MattStarfield/HumidiFire/img/hw01.jpg

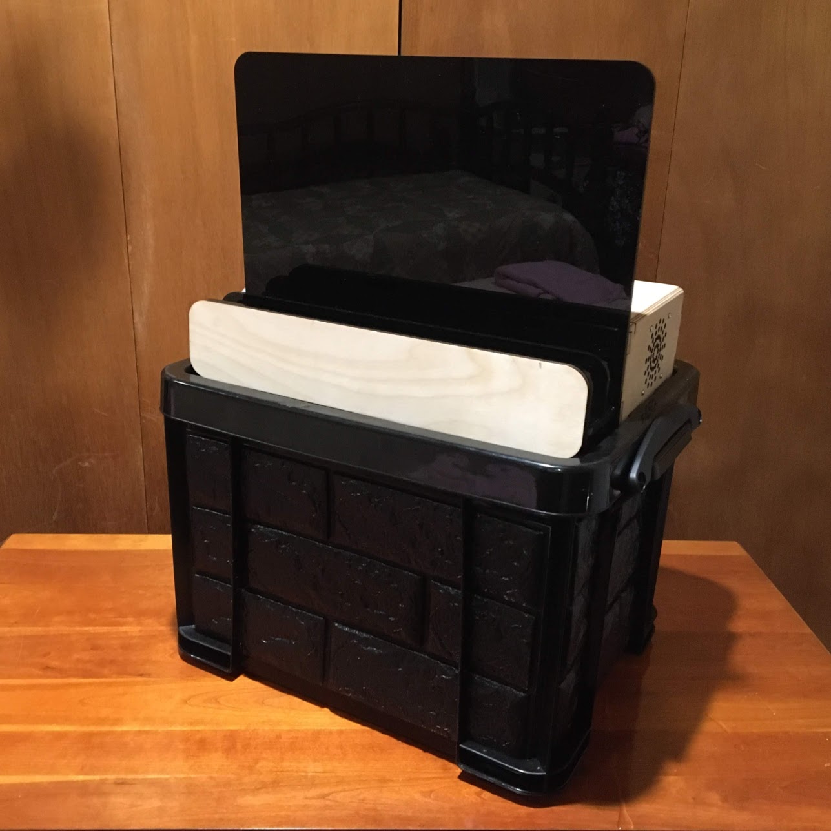
img/hw01.jpg
