MattStarfield/HumidiFire/img/hw02.jpg

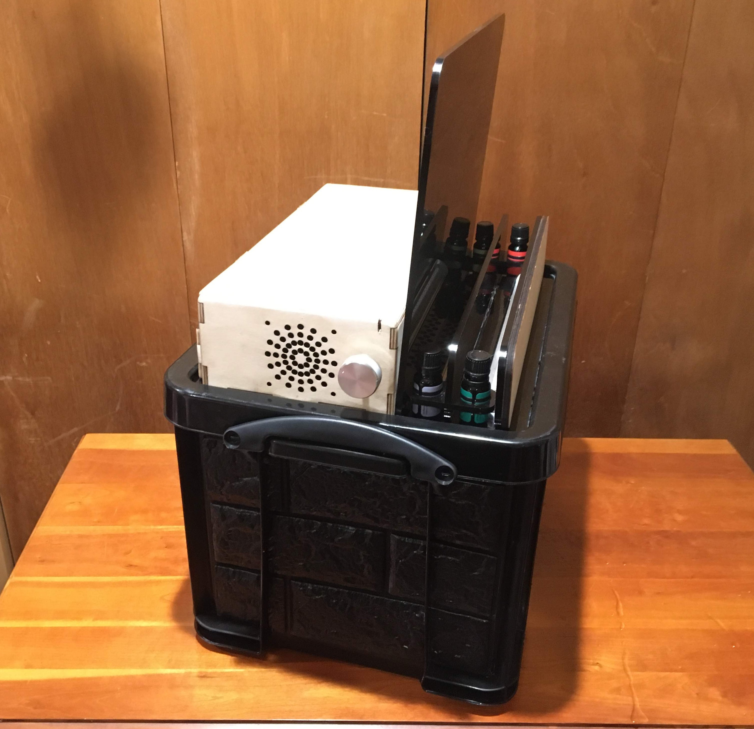
img/hw02.jpg
