MattStarfield/HumidiFire/img/hw03.jpg

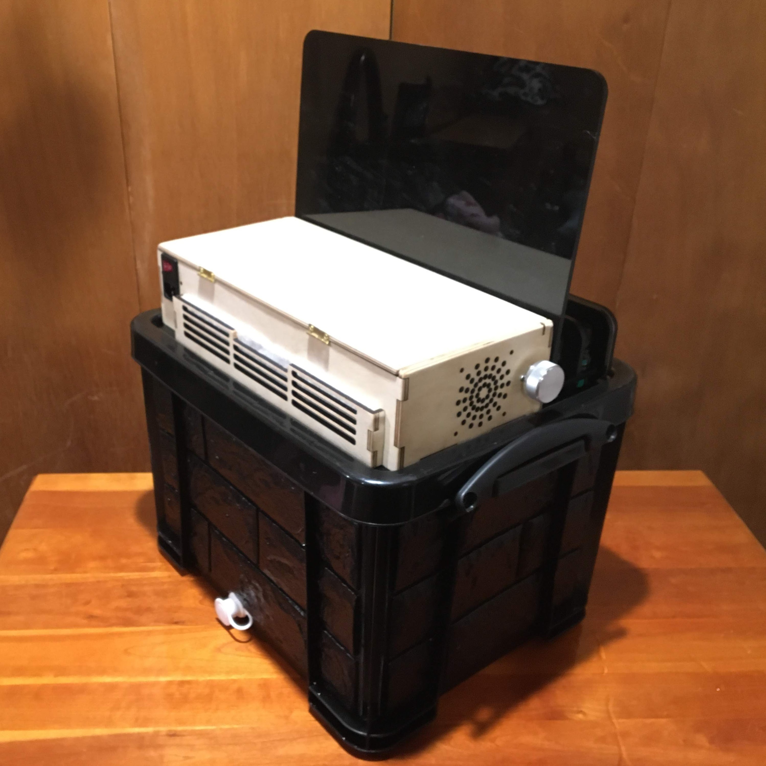
img/hw03.jpg
