MattStarfield/HumidiFire/img/hw04.jpg

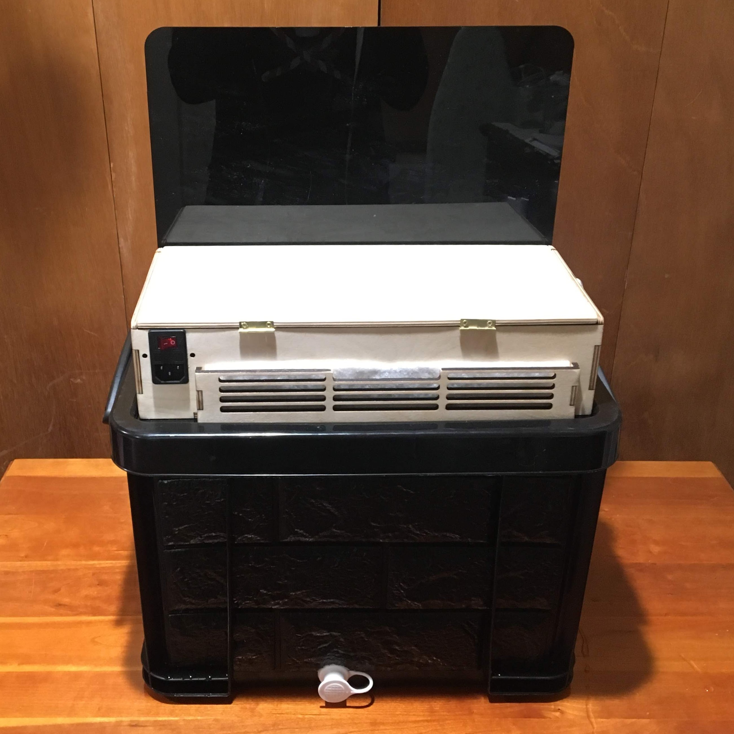
img/hw04.jpg
