MattStarfield/HumidiFire/img/hw05.jpg

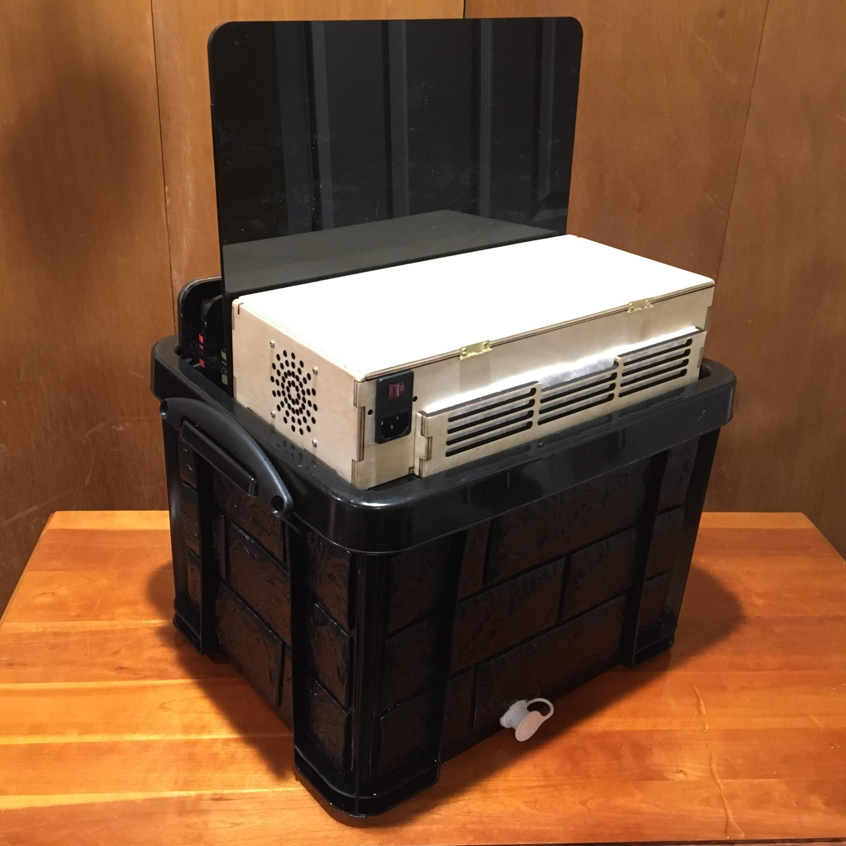
img/hw05.jpg
