MattStarfield/HumidiFire/img/hw06.jpg

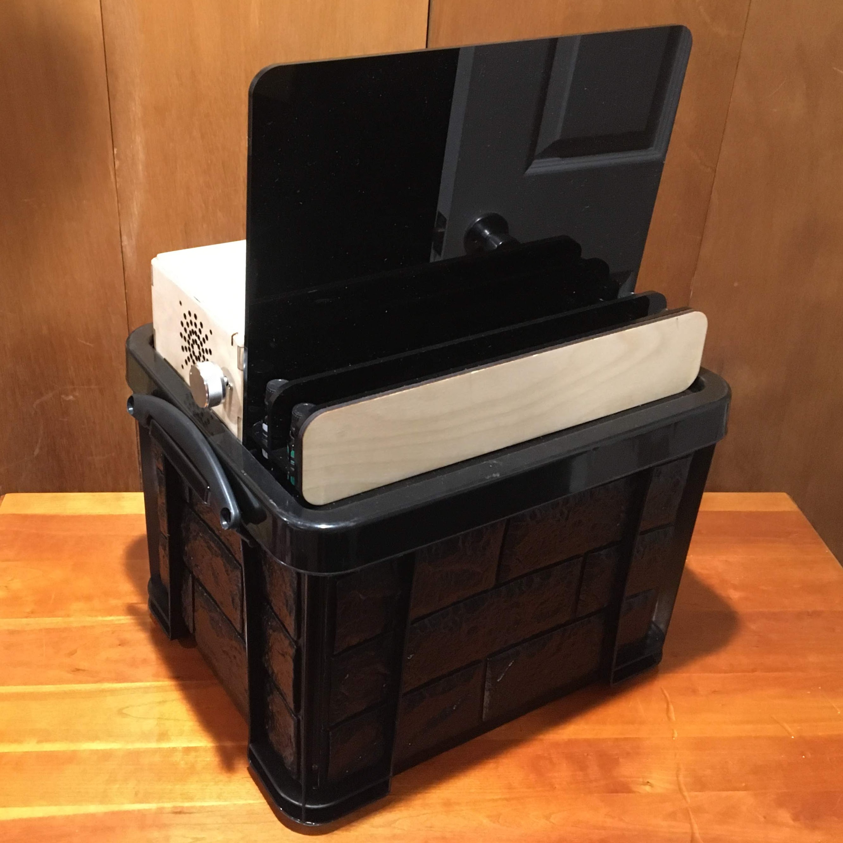
img/hw06.jpg
