MattStarfield/HumidiFire/img/pcb01.jpg

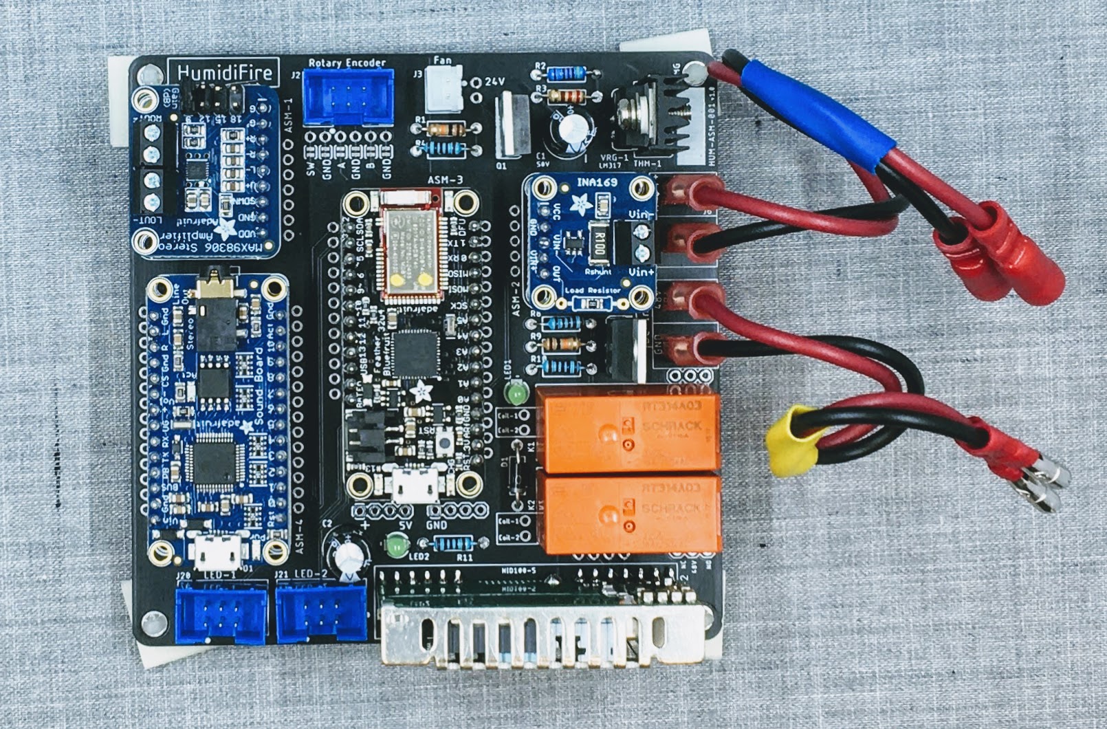
img/pcb01.jpg
