MattStarfield/HumidiFire/img/pcb02.jpg

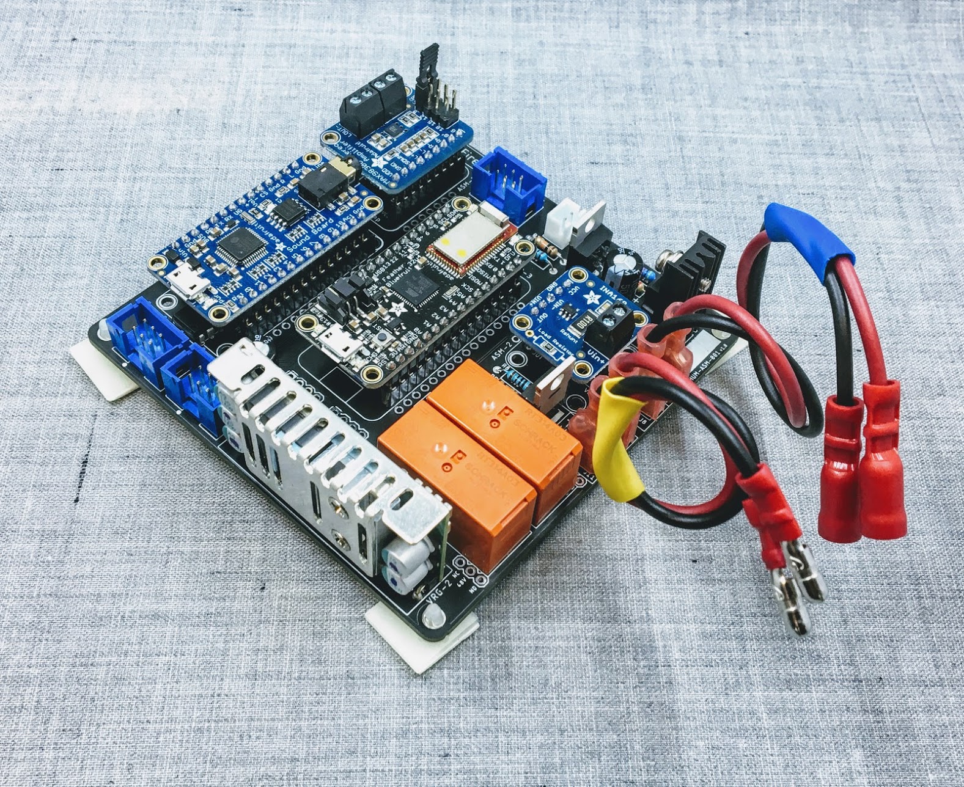
img/pcb02.jpg
