MattStarfield/HumidiFire/img/pcb03.jpg

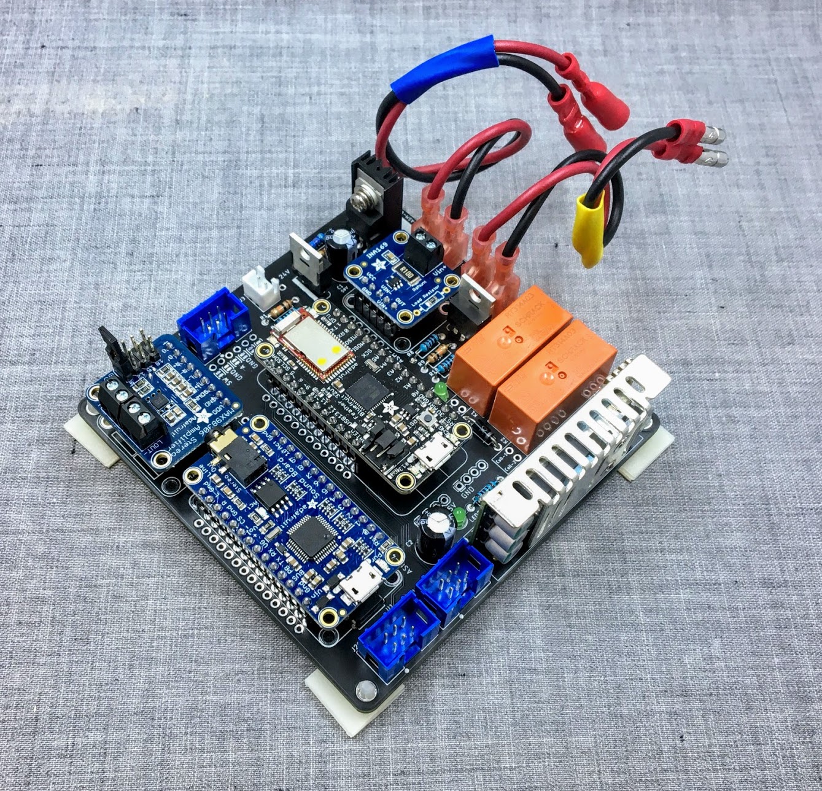
img/pcb03.jpg
