MattStarfield/HumidiFire/img/pcb-cad.png

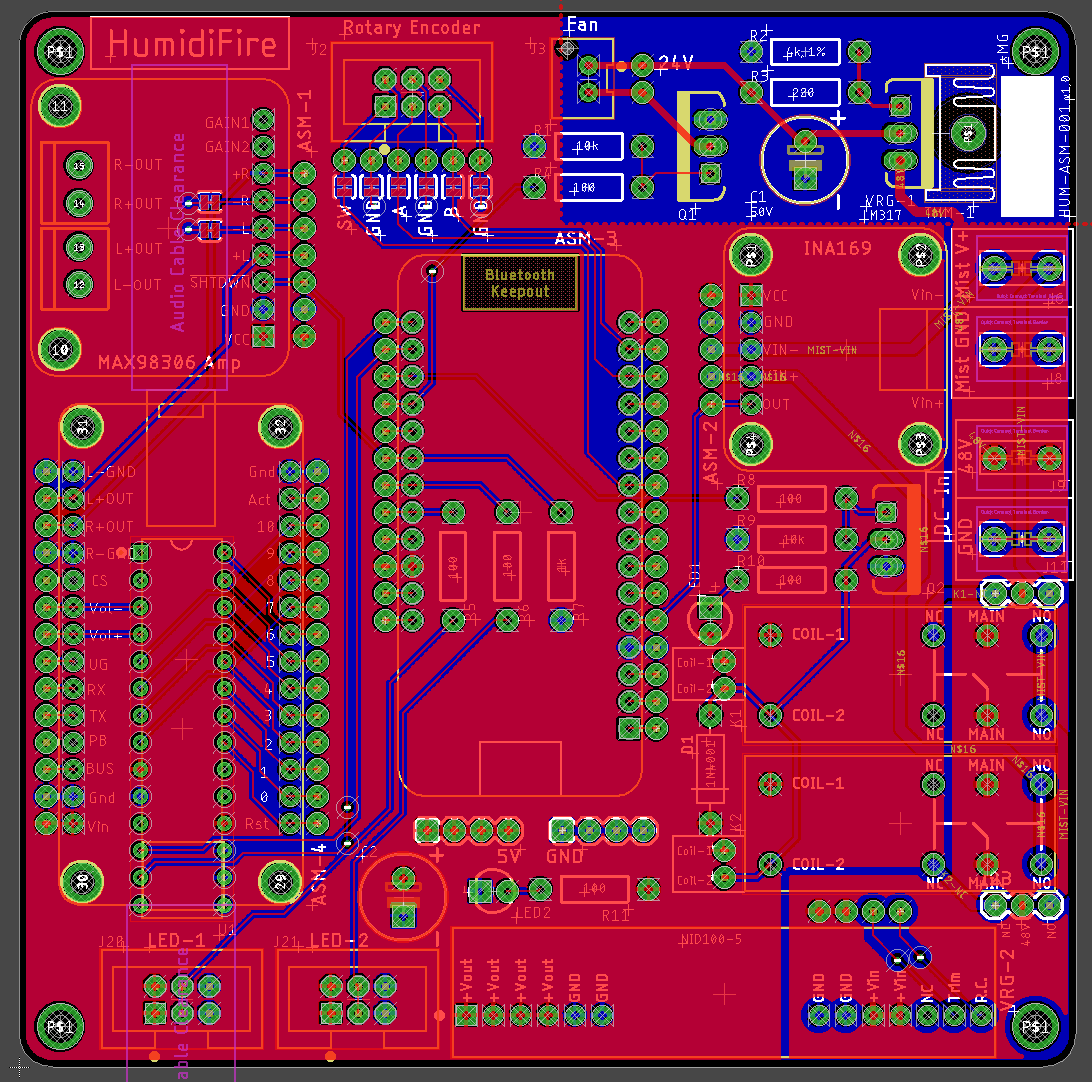
img/pcb-cad.png
