MattStarfield/HumidiFire/img/pcb-render.png

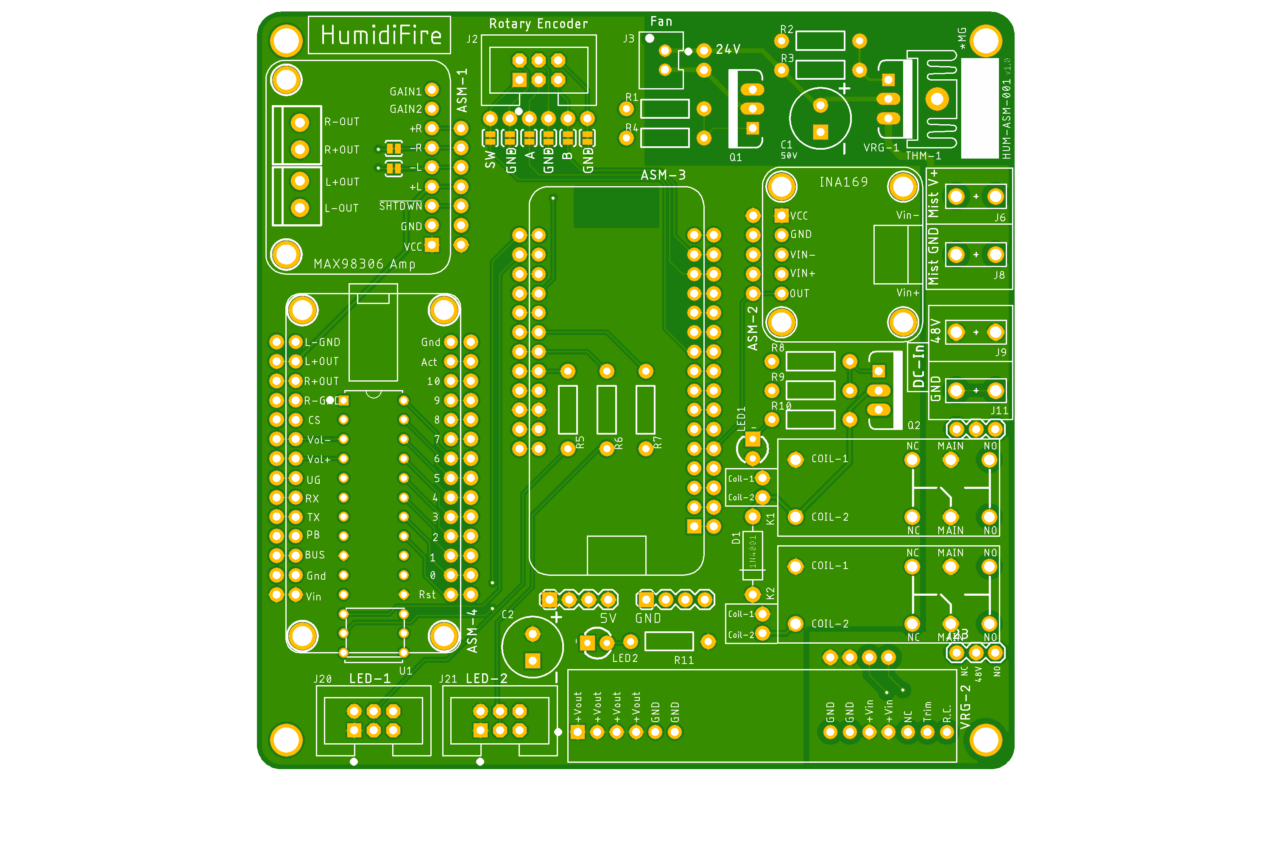
img/pcb-render.png
