MattStarfield/HumidiFire/firmware/examples/jack-o-candle.ino/jack-o-candle.ino.ino

#include <Adafruit_NeoPixel.h>

/*
 5 "flames" of 3 pixels each.
 Each flame can have a brightness of 0 to 254 (play with this scale)
 Eventually, light up center pixel of three first then the sides. This version will just distribute amongst the 3 pixels.

*/

#define PIN 12              // Which pin are those Neopixels hook up to?
#define NUMBER_OF_FLAMES 10 // depends on number of neopixel triplets. 5 for 16 NeoPixel ring. 4 for 12 NeoPixel ring
#define FLAME_WIDTH 1      // How wide are the flames (in LEDs)
#define FLICKER_CHANCE 6   // increase this to increase the chances an individual flame will flicker


// Parameter 1 = number of pixels in strip
// Parameter 2 = pin number (most are valid)
// Parameter 3 = pixel type flags, add together as needed:
//   NEO_KHZ800  800 KHz bitstream (most NeoPixel products w/WS2812 LEDs)
//   NEO_KHZ400  400 KHz (classic 'v1' (not v2) FLORA pixels, WS2811 drivers)
//   NEO_GRB     Pixels are wired for GRB bitstream (most NeoPixel products)
//   NEO_RGB     Pixels are wired for RGB bitstream (v1 FLORA pixels, not v2)
Adafruit_NeoPixel strip = Adafruit_NeoPixel(NUMBER_OF_FLAMES * FLAME_WIDTH, PIN, NEO_GRB + NEO_KHZ800);

uint32_t rez_range = 256*3;
#define D_ false

// console buttons:
struct flame_element{
  int brightness;
  int step;
  int max_brightness;
  long rgb[3];
  byte state;
  } flames[NUMBER_OF_FLAMES];
  
  int new_brightness = 0;
  unsigned long rgb[3]; //reusable temporary array
  uint8_t scaleD_rgb[3];
  byte acc;
 
 #define SCALERVAL 256*3
 const int flamecolors[22][3] = {
{ SCALERVAL, 0,  0},
{ SCALERVAL, 0,  0},
{ SCALERVAL, 0,  0},
{ SCALERVAL, 0,  0},
{ SCALERVAL, 0,  0},
{ SCALERVAL, 0,  0},
{ SCALERVAL, 0,  0},
{ SCALERVAL, 0,  0},
{ SCALERVAL, SCALERVAL*.4,  },
{ SCALERVAL, SCALERVAL*.4,  0},
{ SCALERVAL, SCALERVAL*.4,  0},
{ SCALERVAL, SCALERVAL*.4,  0},
{ SCALERVAL, SCALERVAL*.3,  0},
{ SCALERVAL, SCALERVAL*.3,  0},
{ SCALERVAL, SCALERVAL*.3,  0},
{ SCALERVAL, SCALERVAL*.3,  0},
{ SCALERVAL, SCALERVAL*.3,  0},
{ SCALERVAL, SCALERVAL*.3,  0},
{ SCALERVAL, SCALERVAL*.3,  },
{ SCALERVAL, SCALERVAL*.3,  SCALERVAL}, // white
{ 0, SCALERVAL*.2,  SCALERVAL}, // that one blue flame
{ SCALERVAL,  SCALERVAL*.3,  SCALERVAL*.5}
};

  
  
void setup() {
 // if (D_){
    Serial.begin(9600);
    Serial.println("STARTUP");
//  }
  strip.begin();
  strip.show(); // Initialize all pixels to 'off'
  randomSeed(analogRead(4));
  InitFlames();
  
}

void loop() {

 for(byte flame_count=0; flame_count<NUMBER_OF_FLAMES; flame_count++) {
    switch(flames[flame_count].state){
      case 0: // reset
        CreateNewFlame(flame_count);
      break;
      
      case 1: //increasing
        new_brightness = flames[flame_count].brightness + flames[flame_count].step;
        if (new_brightness > flames[flame_count].max_brightness){
          UpdateFlameColor(flame_count, flames[flame_count].max_brightness);
          flames[flame_count].brightness = flames[flame_count].max_brightness;
          flames[flame_count].step = GetStepSize(); // pick a different speed for flame going out
          flames[flame_count].state = 2;
        } else {
          UpdateFlameColor(flame_count, new_brightness);
          flames[flame_count].brightness = new_brightness;
        }

      break;
      
      
      case 2: //decreasing
        new_brightness = flames[flame_count].brightness - flames[flame_count].step;
        // chance to flicker/rekindle:
        if (random(new_brightness) < FLICKER_CHANCE){
          // rekindle:
          flames[flame_count].state = 1; //increase again
          flames[flame_count].brightness = max(GetMaxBrightness(), flames[flame_count].brightness);
          flames[flame_count].step = GetStepSize(); 
        
        } else {
          if (new_brightness <1){
            flames[flame_count].state = 0; // bottomed out - reset to next flame
            flames[flame_count].brightness = 0;
             UpdateFlameColor(flame_count, 0);
          } else {
            UpdateFlameColor(flame_count, new_brightness);
             flames[flame_count].brightness = new_brightness;
          }
        }
      break;
    }
  
  }
   strip.show();
   delay(22);
  
} //loop()


void InitFlames(){
// Sets initial states in flames array
  for(byte i=0; i<NUMBER_OF_FLAMES; i++) {
    flames[i].state=0;
    
  }
}


void UpdateFlameColor(byte flame_num, int new_brightness){
// 
  uint32_t c = 0;
  uint32_t color_channel_value;
  byte rgb_channel;
  
  new_brightness = min(new_brightness, flames[flame_num].max_brightness);
  

  for(byte rgb_channel=0; rgb_channel<3; rgb_channel++) {
    color_channel_value = flames[flame_num].rgb[rgb_channel];
    color_channel_value = color_channel_value * (uint32_t)new_brightness; // keep it long
    color_channel_value = color_channel_value/(uint32_t)rez_range;
    rgb[rgb_channel] = max(0L,color_channel_value);
  } // step through R G B



  // spread possible values of 0 - 768 across 3 pixels
  for(byte sub_pixel=0; sub_pixel<FLAME_WIDTH; sub_pixel++) {
    for(byte i=0; i<3; i++) { // rgb
      acc = rgb[i]/3;
      byte d = rgb[i]%3;
      if (sub_pixel < d){
        acc++;
      }
      scaleD_rgb[i] = acc;
      
    }
    c = strip.Color(scaleD_rgb[0],scaleD_rgb[1], scaleD_rgb[2]);
    strip.setPixelColor(flame_num * FLAME_WIDTH + sub_pixel, c);
  }
  
}


void CreateNewFlame(byte flame_num){
  flames[flame_num].step = GetStepSize();
 flames[flame_num].max_brightness = GetMaxBrightness();

  flames[flame_num].brightness = 0;
  flames[flame_num].state = 1;
  byte color_index = random(22);
  for(byte i=0; i<3; i++) {
    flames[flame_num].rgb[i] = flamecolors[color_index][i];
  }
 
}

int GetStepSize(){
   return random(70)+1;
}
int GetMaxBrightness(){
  int retVal;
//  retVal = random(rez_range/4) +  random(rez_range/4) + random(rez_range/4) + rez_range/4 +1; // bell curve
//  retVal = random(rez_range*3/4) +  rez_range/4; // flat distribution
    retVal = random(rez_range/2) +  rez_range/2; // brighter flat distribution
    return retVal;
}
